antmicro/flickerless-led-driver/assets/previews/layer1_thumbnail.png

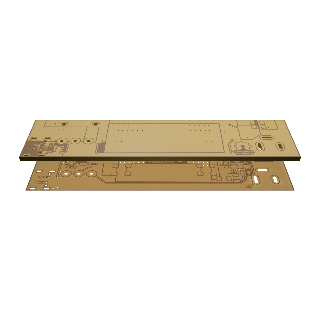
assets/previews/layer1_thumbnail.png
