antmicro/flickerless-led-driver/assets/previews/layer2.png

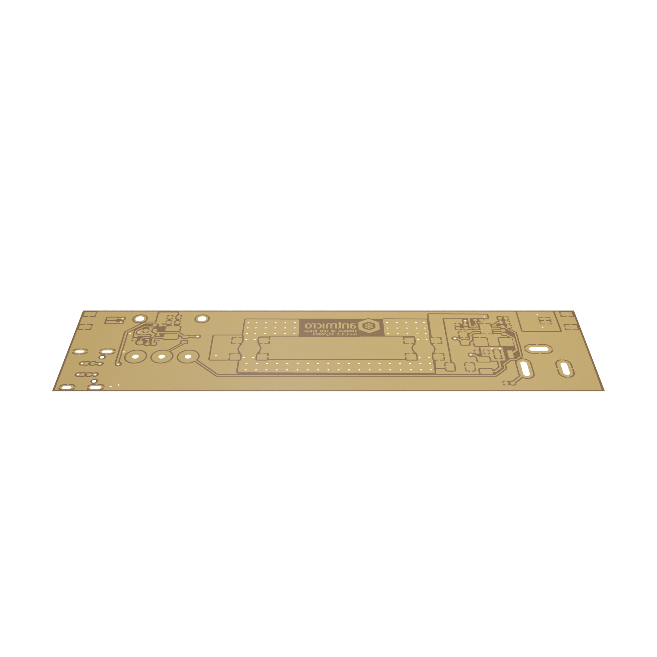
assets/previews/layer2.png
