antmicro/flickerless-led-driver/assets/previews/leftT.png

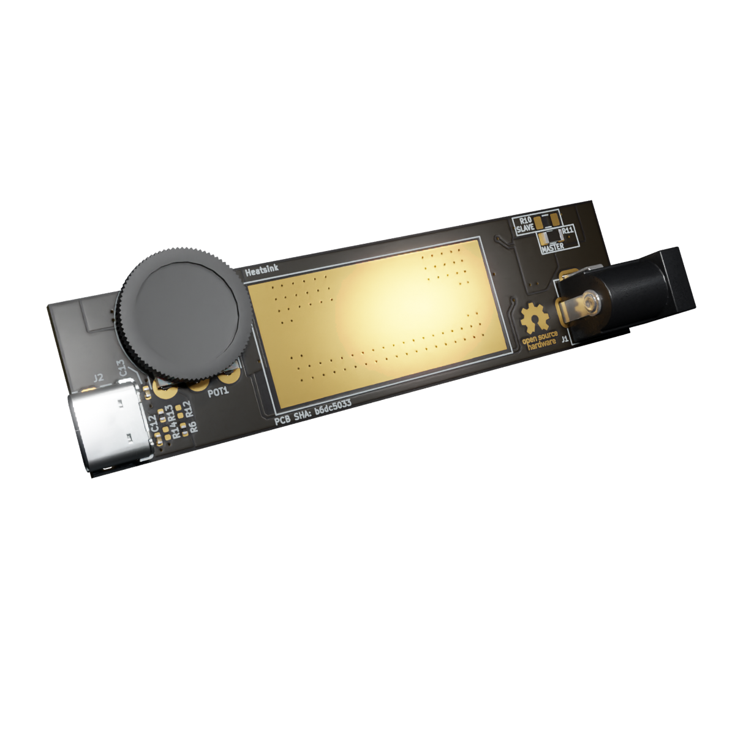
assets/previews/leftT.png
