antmicro/flickerless-led-driver/assets/previews/orthoB.png

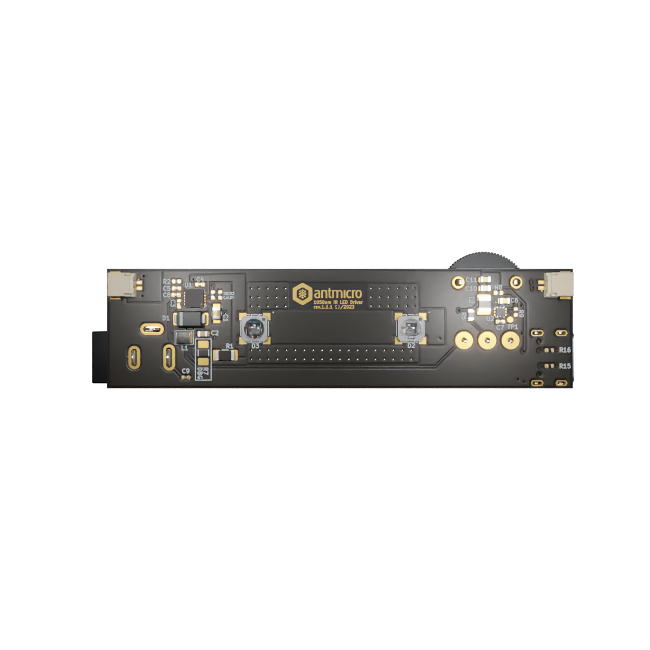
assets/previews/orthoB.png
