antmicro/flickerless-led-driver/assets/previews/photoB.png

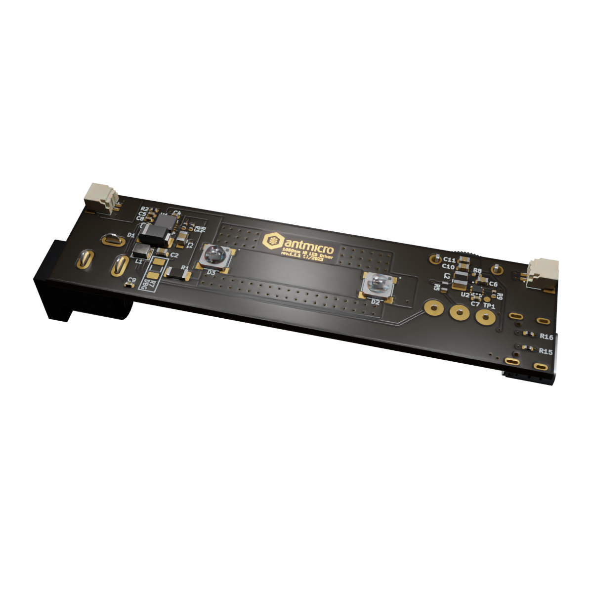
assets/previews/photoB.png
