antmicro/flickerless-led-driver/assets/previews/photoT.png

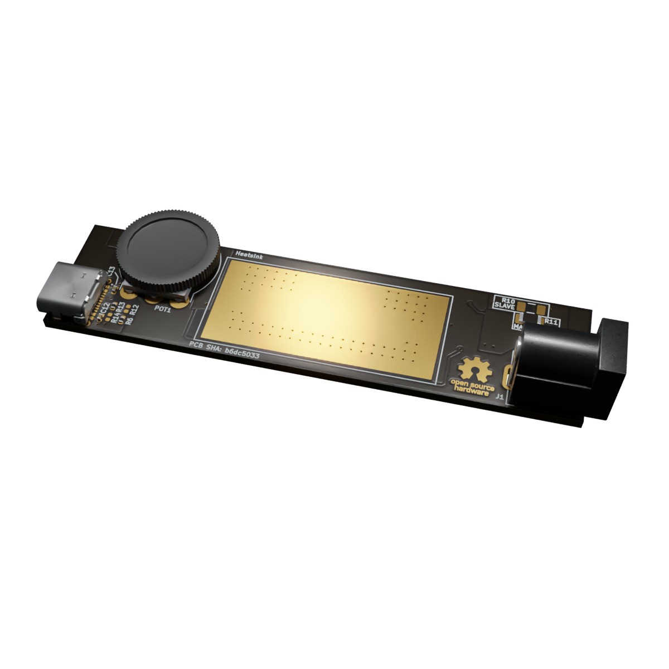
assets/previews/photoT.png
