antmicro/flickerless-led-driver/assets/previews/rightB.png

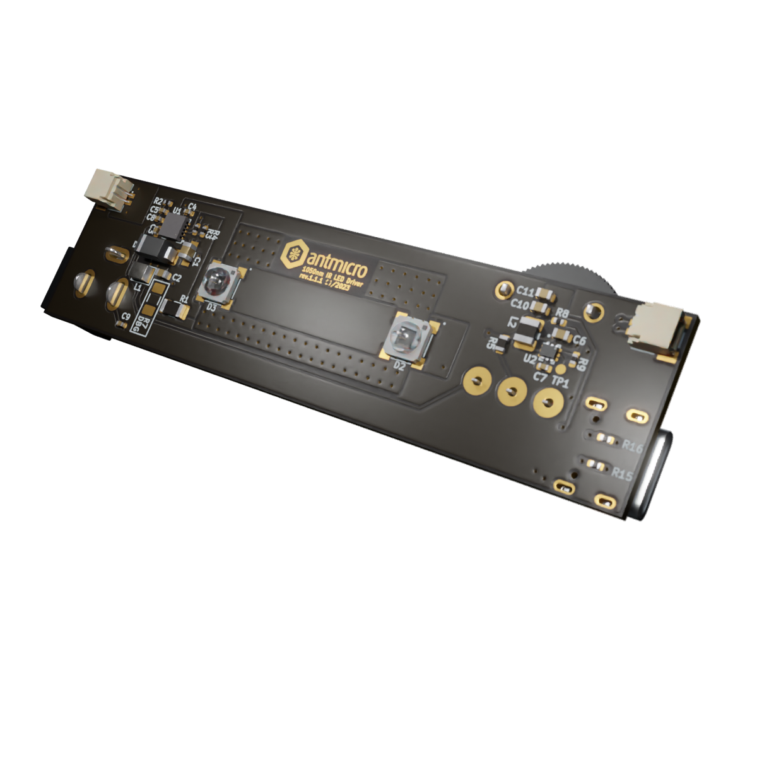
assets/previews/rightB.png
