antmicro/flickerless-led-driver/assets/previews/rightT.png

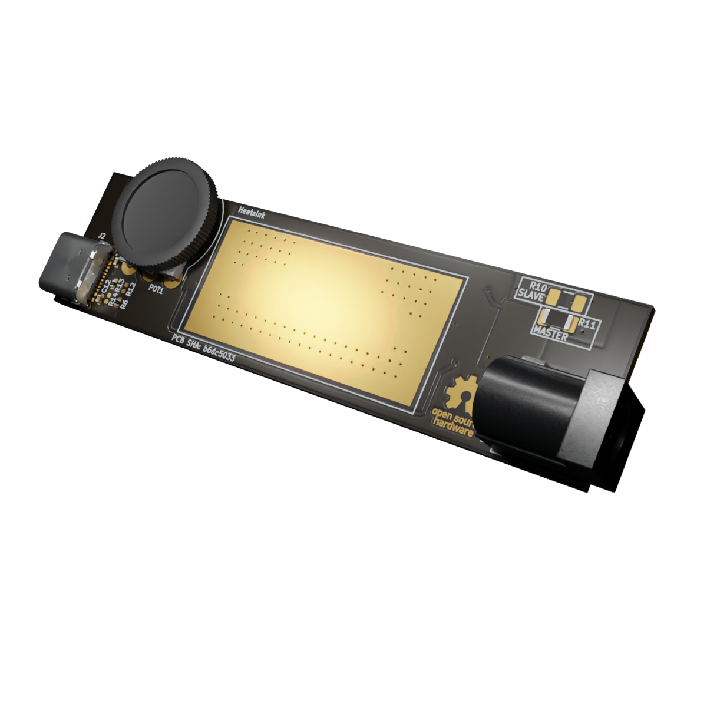
assets/previews/rightT.png
